arildj78/GettingToBlinky/LTspice/astable.asc

C1: cap; 470µ
C2: cap; 0.01µ
C3: cap; 0.01µ
C4: cap; 1µ
C5: cap; 470µ
D2: LED; L1C1-AMB1000000000
R1: res; 180
R2: res; 1500
R3: res; 100
R5: res; 8
U1: NE555
V1: voltage; 5
Named nets: 0, +5V, out, thr, disch
.tran 5
